pe1mew/lasermaze-game/develeopmentAndResearch-documentation/inspiration/2018-08-10 10.21.51.jpg

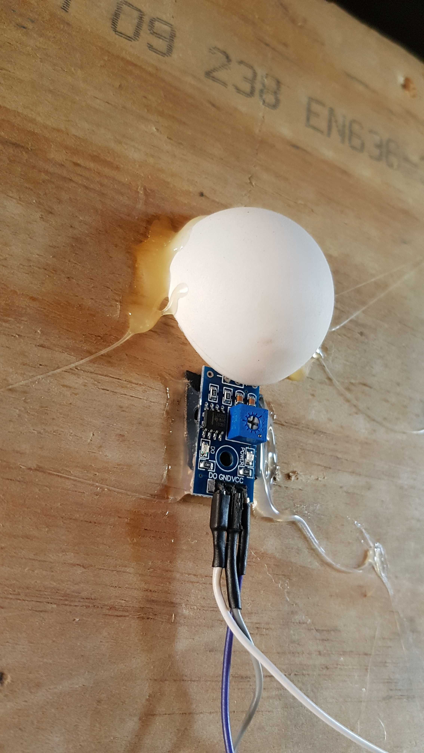
develeopmentAndResearch-documentation/inspiration/2018-08-10 10.21.51.jpg
