pe1mew/lasermaze-game/develeopmentAndResearch-documentation/inspiration/2018-08-10 10.22.36.jpg

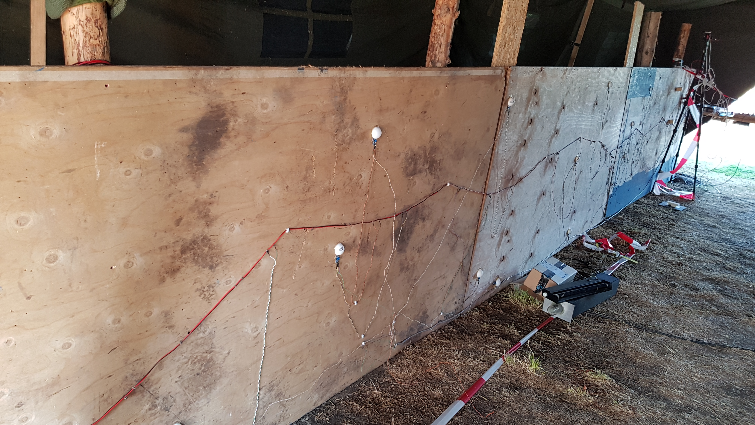
develeopmentAndResearch-documentation/inspiration/2018-08-10 10.22.36.jpg
