pe1mew/lasermaze-game/develeopmentAndResearch-documentation/inspiration/2018-08-13 13.50.18.jpg

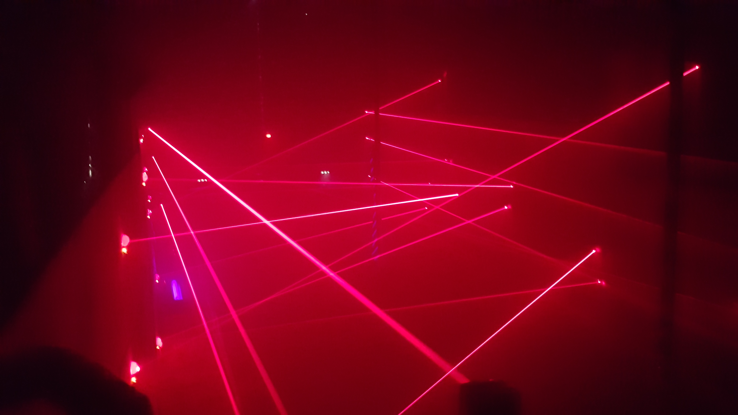
develeopmentAndResearch-documentation/inspiration/2018-08-13 13.50.18.jpg
