pe1mew/lasermaze-game/LaserTransmitterReceivers/3d/laserReceptor/LaserMazeReceptor_020_leftBottom.png

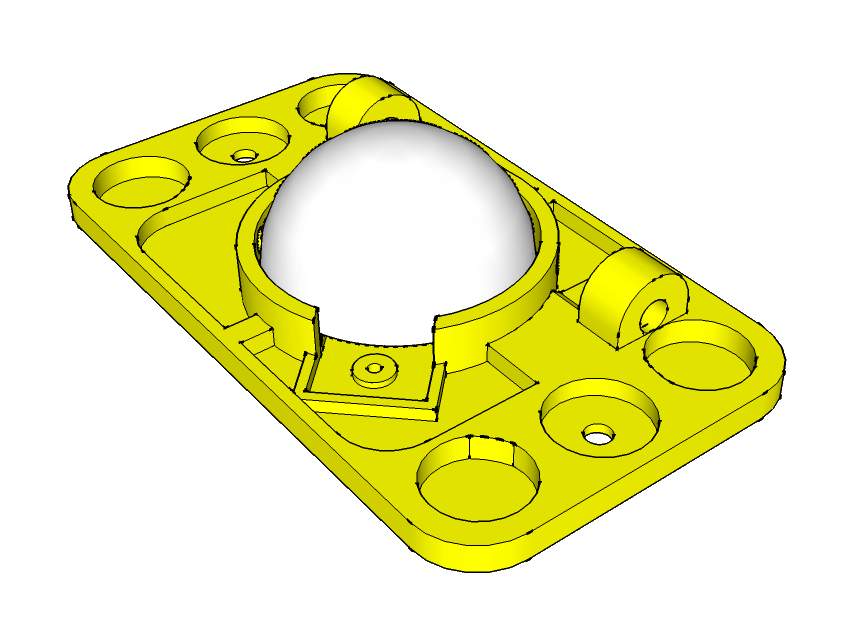
LaserTransmitterReceivers/3d/laserReceptor/LaserMazeReceptor_020_leftBottom.png
