pe1mew/lasermaze-game/LaserTransmitterReceivers/Arduino/ESP8266GPIOTXControllerRelay/PE1MEW_Timer.h

/*--------------------------------------------------------------------
  This file is part of the PE1MEW TTNMapper node.
  
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
  The PE1MEW TTNMapper node is distributed in the hope that 
  it will be useful, but WITHOUT ANY WARRANTY; without even the 
  implied warranty of MERCHANTABILITY or FITNESS FOR A PARTICULAR 
  PURPOSE.
  --------------------------------------------------------------------*/

/*!
   
 \file PE1MEW_Timer.h
 \brief Simple expiry timer 
 \date 10-1-2019
 \author Remko Welling (PE1MEW) 
 \version 1.2
 
 Version | comment
 --------|--------
 1.2     | Sanity check of C++ code
 1.1     | Modified set() to setExpiry()
 1.0     | Initial version
 
 */
#ifndef __PE1MEW_TIMER_H_
#define __PE1MEW_TIMER_H_

#include <stdint.h>
#include <arduino.h>  // millis()

/// \brief Timer class
class PE1MEW_Timer
{
//variables
public:
protected:
private:

  /// end time at which timer shall expire
  unsigned long _msEndTime;

  /// State of the timer, true = running, false = expired.
  bool _active;
   
//functions
public:
	PE1MEW_Timer();

	~PE1MEW_Timer();

  /// \brief Set timer
  /// Set time in milliseconds in the future from now that the time shall expire
  /// \retval true = Timer ste successfully, false = Timer is running and not set.
  bool setExpiry(uint32_t msTime);

  /// \brief test if timer has expired.
  /// \retval true = Timer is expired, false = Timer is not expired.
  bool getExpired();
	
protected:
private:
}; // PE1MEW_Timer

#endif //__PE1MEW_TIMER_H_
